eshazen/carputer/Case/standoff_test.stl

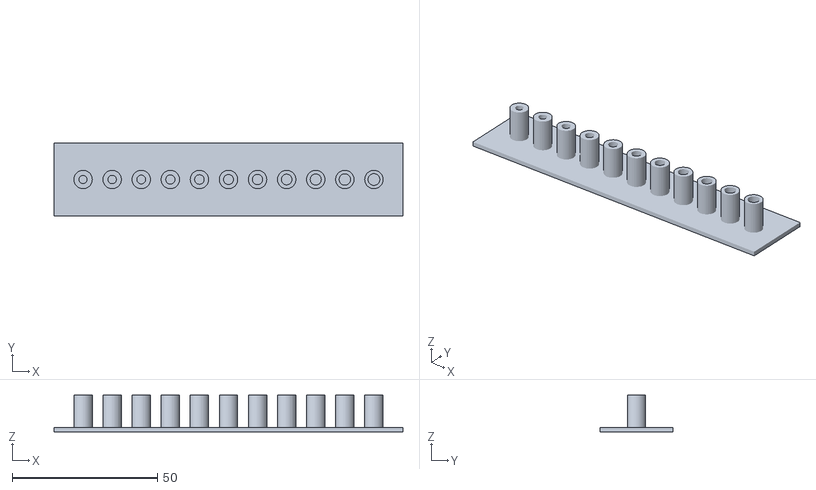
[picture p15: CAD file, 2025-10-08]
Case/standoff_test.stl
120.0 x 25.0 x 12.7
