eshazen/carputer/Case/box_fast.stl

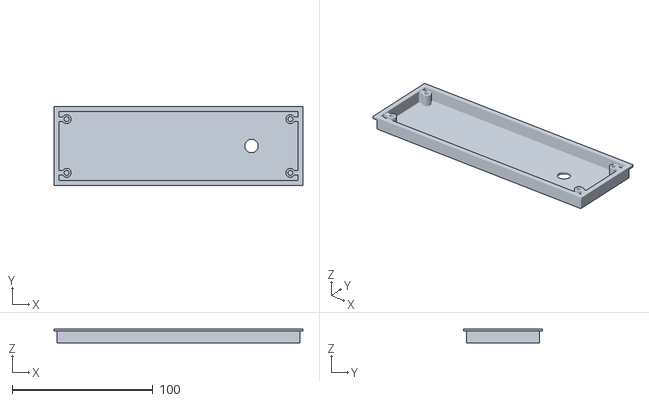
[picture p16: CAD file, 2025-10-08]
Case/box_fast.stl
176.7 x 56.1 x 10.0
