eshazen/carputer/Case/new_mount.3mf

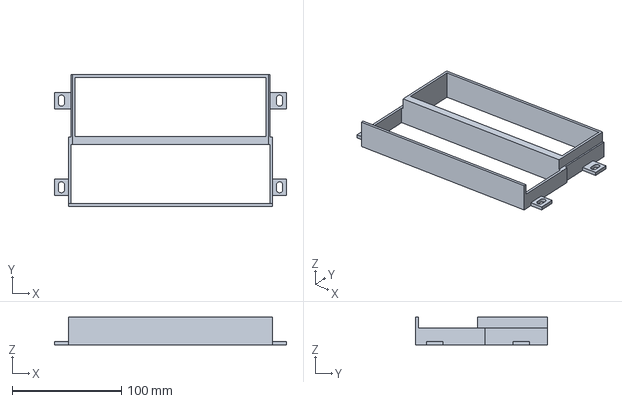
[picture p17: CAD file, 2025-09-20]
Case/new_mount.3mf
212.5 x 120.7 x 25.4 mm
