eshazen/carputer/Case/Unnamed-MKRZero_V5.0.stl

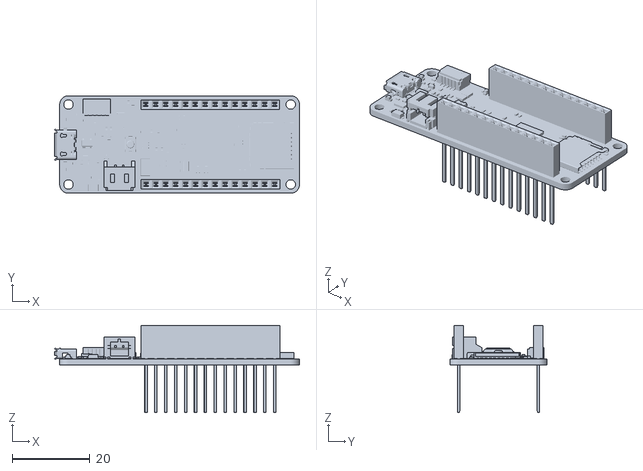
[picture p18: CAD file, 2025-09-15]
Case/Unnamed-MKRZero_V5.0.stl
62.8 x 25.0 x 22.4
