eshazen/carputer/Case/mount.stl

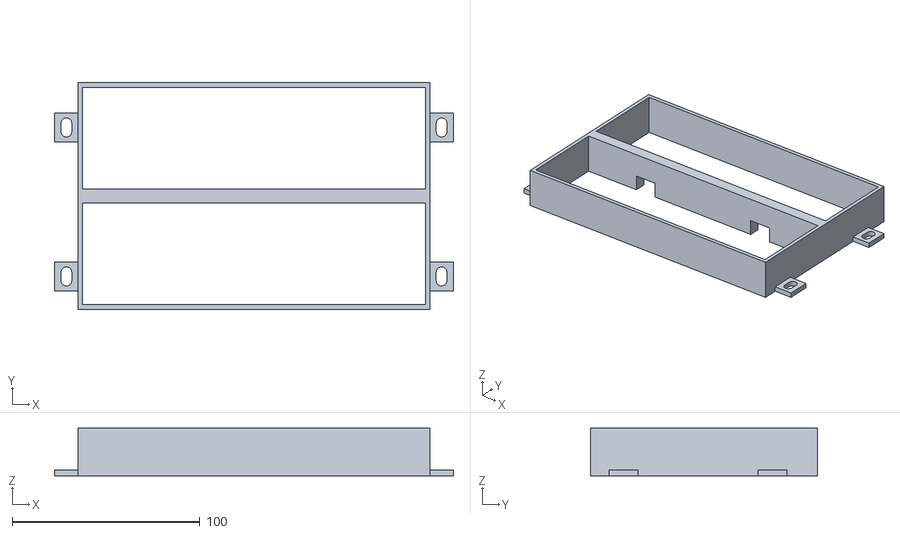
[picture p19: CAD file, 2025-09-15]
Case/mount.stl
212.5 x 120.7 x 25.4
