eshazen/carputer/Case/din.3mf

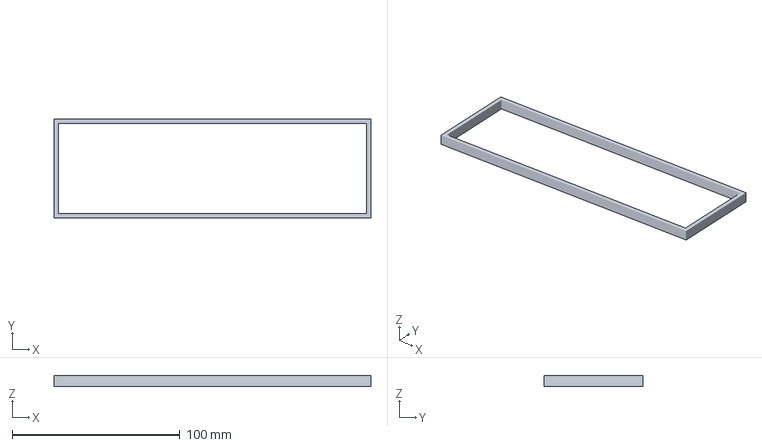
[picture p20: CAD file, 2025-09-14]
Case/din.3mf
189.2 x 59.1 x 6.35 mm
