eshazen/carputer/Case/mount2.stl

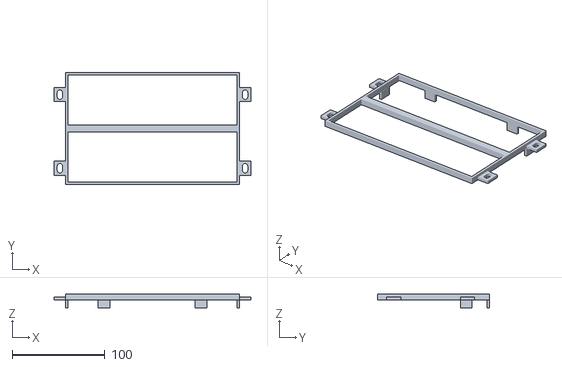
[picture p21: CAD file, 2025-09-14]
Case/mount2.stl
212.5 x 120.7 x 15.1
