eshazen/carputer/Data/Tools/test/GRID.CSV

NumLat | LatMin | LatMax | LatStep | NumLon | LonMin | LonMax | LonStep
52 | 24 | 49.5 | 0.5 | 119 | -125 | -66 | 0.5
