eshazen/carputer/Data/Tools/test/TOWN.CSV

1 | Key West | FL | 24.565063 | -81.775539 | 1 | 86
1 | Big Coppitt Key | FL | 24.580225 | -81.652178 | 1 | 86
1 | Stock Island | FL | 24.56399 | -81.739793 | 1 | 86
1 | Marathon | FL | 24.732338 | -81.025122 | 1 | 87
1 | Key Colony Beach | FL | 24.723406 | -81.021647 | 1 | 87
1 | Cudjoe Key | FL | 24.67875 | -81.499676 | 1 | 87
1 | Big Pine Key | FL | 24.685136 | -81.362518 | 1 | 87
1 | Islamorada, Village of Islands | FL | 24.984352 | -80.543296 | 1 | 88
1 | Layton | FL | 24.825131 | -80.811624 | 1 | 88
1 | Duck Key | FL | 24.772765 | -80.90952 | 1 | 88
1 | Homestead | FL | 25.465912 | -80.445993 | 2 | 89
1 | Florida City | FL | 25.444071 | -80.467665 | 2 | 89
1 | Homestead Base | FL | 25.49328 | -80.39022 | 2 | 89
1 | Key Largo | FL | 25.122584 | -80.411571 | 2 | 89
1 | North Key Largo | FL | 25.260754 | -80.321566 | 2 | 89
1 | Leisure City | FL | 25.493935 | -80.436093 | 2 | 89
1 | Tavernier | FL | 25.026449 | -80.499702 | 2 | 89
1 | San Pedro | TX | 25.981339 | -97.588211 | 3 | 54
1 | Brownsville | TX | 25.989404 | -97.480626 | 3 | 55
1 | Cameron Park | TX | 25.97141 | -97.478173 | 3 | 55
1 | Reid Hope King | TX | 25.921294 | -97.414761 | 3 | 55
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
