eshazen/carputer/Data/Tools/test2/TOWN.CSV

2 | Key West | FL | 24.565063 | -81.775539 | 1 | 86
2 | Big Coppitt Key | FL | 24.580225 | -81.652178 | 1 | 86
2 | Stock Island | FL | 24.56399 | -81.739793 | 1 | 86
2 | Marathon | FL | 24.732338 | -81.025122 | 1 | 87
2 | Key Colony Beach | FL | 24.723406 | -81.021647 | 1 | 87
2 | Cudjoe Key | FL | 24.67875 | -81.499676 | 1 | 87
2 | Big Pine Key | FL | 24.685136 | -81.362518 | 1 | 87
2 | Islamorada, Village of Islands | FL | 24.984352 | -80.543296 | 1 | 88
2 | Layton | FL | 24.825131 | -80.811624 | 1 | 88
2 | Duck Key | FL | 24.772765 | -80.90952 | 1 | 88
2 | Homestead | FL | 25.465912 | -80.445993 | 2 | 89
2 | Florida City | FL | 25.444071 | -80.467665 | 2 | 89
2 | Homestead Base | FL | 25.49328 | -80.39022 | 2 | 89
2 | Key Largo | FL | 25.122584 | -80.411571 | 2 | 89
2 | North Key Largo | FL | 25.260754 | -80.321566 | 2 | 89
2 | Leisure City | FL | 25.493935 | -80.436093 | 2 | 89
2 | Tavernier | FL | 25.026449 | -80.499702 | 2 | 89
2 | San Pedro | TX | 25.981339 | -97.588211 | 3 | 54
2 | Brownsville | TX | 25.989404 | -97.480626 | 3 | 55
2 | Cameron Park | TX | 25.97141 | -97.478173 | 3 | 55
2 | Reid Hope King | TX | 25.921294 | -97.414761 | 3 | 55
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
