eshazen/carputer/Arduino/WhyNoDisplay/WhyNoDisplay.ino

//
// display test
//
#define USE_ENC

#include <math.h>
#include <SD.h>
#include <string.h>

#include "oled.h"

#ifdef USE_ENC
#include "encoder.h"
#define TIMER_INTERVAL_MS 4
#include "timer_setup.h"
// Init selected SAMD timer
SAMDTimer ITimer(SELECTED_TIMER);
volatile int tock = 0;

void TimerHandler()
{
  encoder->tick();
  ++tock;
}
#endif

void oled_print( int line, const char *str) {
  if( line < USE_LINES) {
    draw_text( oledBuf, str, 1, (line+1) * LINE_SPC, 15);
    send_buffer_to_OLED( oledBuf, 0, 0);
  }
}

void setup() {

  Serial.begin(9600);
  while (!Serial) {
    ;
  }

#ifdef USE_ENC
  encoder_setup();

  // Interval in millisecs
  if (!ITimer.attachInterruptInterval_MS(TIMER_INTERVAL_MS, TimerHandler)) {
    Serial.println(F("Can't set ITimer. Select another freq. or timer"));
    while(1)
      ;
  }
  
#endif  

  delay(500);

  SSD1322_HW_Init();
  SSD1322_API_init();
  select_font( &FreeMono9pt7b);

  delay(500);

  pinMode( LED_BUILTIN, OUTPUT);

  fill_buffer( oledBuf, 0);		// clear screen
  oled_print( 0, "Display Test 1.0");
  Serial.println("Test 1.0");
  delay(1000);

  fill_buffer( oledBuf, 0);		// clear screen
  oled_print( 0, "Display Test 1.1");
  Serial.println("Test 1.0");
  delay(1000);

  fill_buffer( oledBuf, 0);		// clear screen
  oled_print( 0, "Display Test 1.2");
  Serial.println("Test 1.0");
  delay(1000);

} // setup()

int fake_time = 0;
char gpsFake[32];
char buff[32];

void loop() {

  const char *gpsTime;

  fake_time++;
  snprintf( gpsFake, sizeof(gpsFake), "T%d", fake_time);
  gpsTime = gpsFake;

  Serial.println( gpsTime);
  oled_print( 1, gpsTime);

#ifdef USE_ENC
  int newPos = encoder->getPosition();
  Serial.print(tock);
  Serial.print("  ");
  Serial.println(newPos);
  digitalWrite( ENC_RED, newPos & 1);
  digitalWrite( ENC_GRN, newPos & 2);

  snprintf( buff, sizeof(buff), "Enc [%d]", newPos);
  oled_print( 2, buff);
#endif

  delay(1000);


} // loop()
