eshazen/carputer/Arduino/WhyNoDisplay/timer_setup.h

#if !( defined(ARDUINO_SAMD_ZERO) || defined(ARDUINO_SAMD_MKR1000) || defined(ARDUINO_SAMD_MKRWIFI1010) \
      || defined(ARDUINO_SAMD_NANO_33_IOT) || defined(ARDUINO_SAMD_MKRFox1200) || defined(ARDUINO_SAMD_MKRWAN1300) || defined(ARDUINO_SAMD_MKRWAN1310) \
      || defined(ARDUINO_SAMD_MKRGSM1400) || defined(ARDUINO_SAMD_MKRNB1500) || defined(ARDUINO_SAMD_MKRVIDOR4000) \
      || defined(ARDUINO_SAMD_CIRCUITPLAYGROUND_EXPRESS) || defined(__SAMD51__) || defined(__SAMD51J20A__) \
      || defined(__SAMD51J19A__) || defined(__SAMD51G19A__) || defined(__SAMD51P19A__)  \
      || defined(__SAMD21E15A__) || defined(__SAMD21E16A__) || defined(__SAMD21E17A__) || defined(__SAMD21E18A__) \
      || defined(__SAMD21G15A__) || defined(__SAMD21G16A__) || defined(__SAMD21G17A__) || defined(__SAMD21G18A__) \
      || defined(__SAMD21J15A__) || defined(__SAMD21J16A__) || defined(__SAMD21J17A__) || defined(__SAMD21J18A__) )
  #error This code is designed to run on SAMD21/SAMD51 platform! Please check your Tools->Board setting.
#endif

/////////////////////////////////////////////////////////////////

// These define's must be placed at the beginning before #include "SAMDTimerInterrupt.h"
// _TIMERINTERRUPT_LOGLEVEL_ from 0 to 4
// Don't define _TIMERINTERRUPT_LOGLEVEL_ > 0. Only for special ISR debugging only. Can hang the system.
// Don't define TIMER_INTERRUPT_DEBUG > 2. Only for special ISR debugging only. Can hang the system.
#define TIMER_INTERRUPT_DEBUG         0
#define _TIMERINTERRUPT_LOGLEVEL_     0

// Select only one to be true for SAMD21. Must must be placed at the beginning before #include "SAMDTimerInterrupt.h"
#define USING_TIMER_TC3         true      // Only TC3 can be used for SAMD51
#define USING_TIMER_TC4         false     // Not to use with Servo library
#define USING_TIMER_TC5         false
#define USING_TIMER_TCC         false
#define USING_TIMER_TCC1        false
#define USING_TIMER_TCC2        false     // Don't use this, can crash on some boards

// Uncomment To test if conflict with Servo library
//#include "Servo.h"

/////////////////////////////////////////////////////////////////

// To be included only in main(), .ino with setup() to avoid `Multiple Definitions` Linker Error
#include "SAMDTimerInterrupt.h"

#ifndef LED_BUILTIN
  #define LED_BUILTIN       13
#endif

volatile uint32_t preMillisTimer = 0;

//////////////////////////////////////////////

// TC3, TC4, TC5 max permissible TIMER_INTERVAL_MS is 1398.101 ms, larger will overflow, therefore not permitted
// Use TCC, TCC1, TCC2 for longer TIMER_INTERVAL_MS

volatile uint32_t preMillisTimer1 = 0;

#if USING_TIMER_TC3
  #define SELECTED_TIMER      TIMER_TC3
#elif USING_TIMER_TC4
  #define SELECTED_TIMER      TIMER_TC4
#elif USING_TIMER_TC5
  #define SELECTED_TIMER      TIMER_TC5
#elif USING_TIMER_TCC
  #define SELECTED_TIMER      TIMER_TCC
#elif USING_TIMER_TCC1
  #define SELECTED_TIMER      TIMER_TCC1
#elif USING_TIMER_TCC2
  #define SELECTED_TIMER      TIMER_TCC
#else
  #error You have to select 1 Timer  
#endif
